HelloAlex4/Maturitaetsarbeit-Design-and-Development-of-a-Portable-Stereoscopic-Wigglegram-Camera/PCBs/mainPCB/PCB_Layout.png

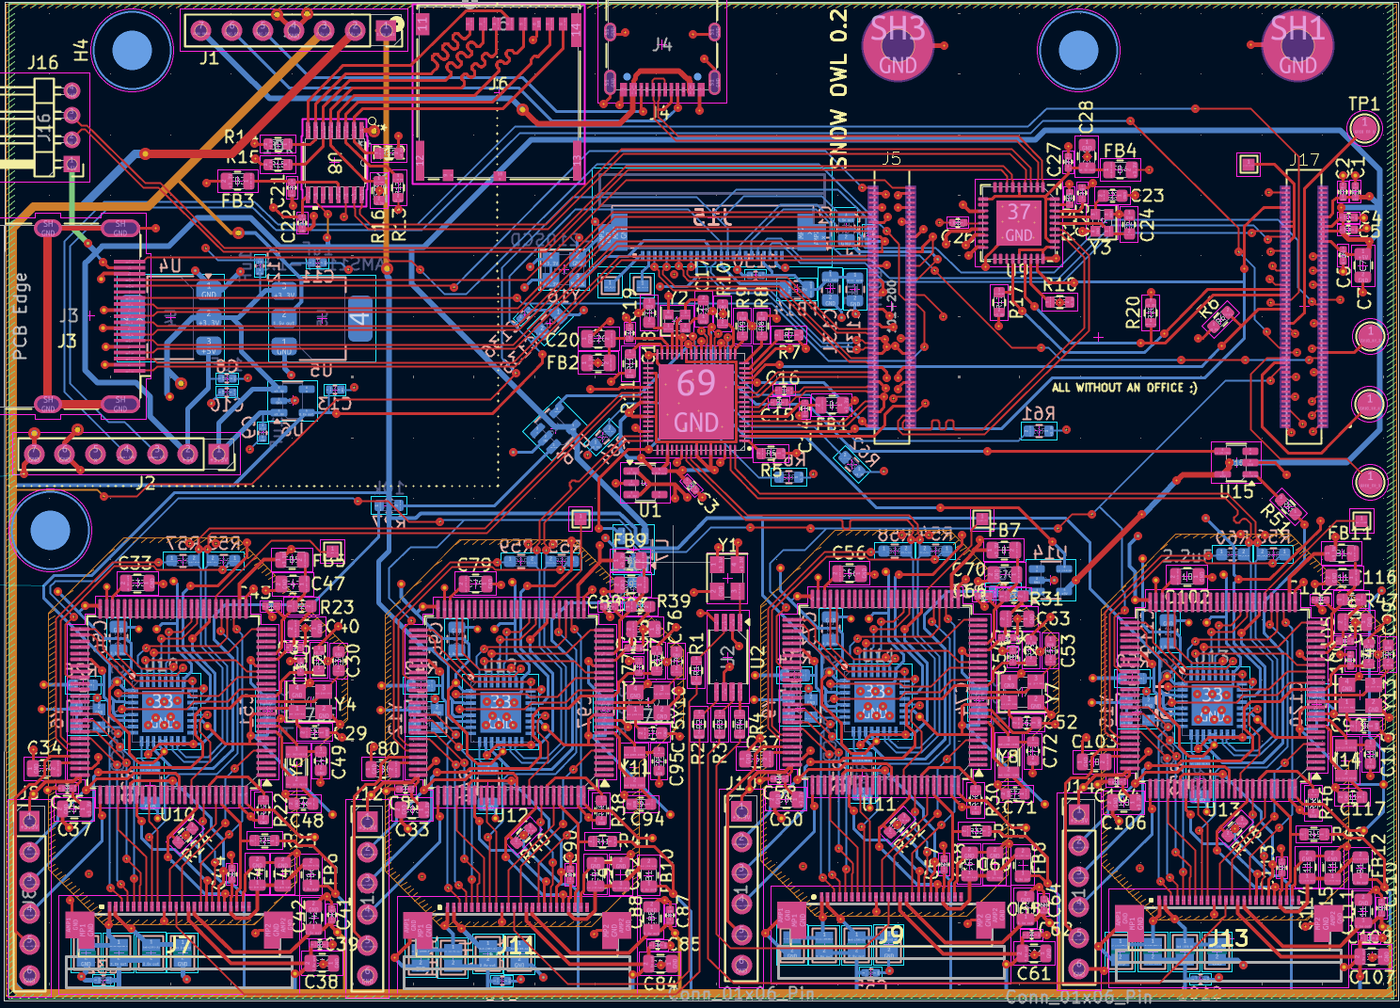
PCBs/mainPCB/PCB_Layout.png
