HelloAlex4/Maturitaetsarbeit-Design-and-Development-of-a-Portable-Stereoscopic-Wigglegram-Camera/sample_Images/wigglegram2.gif

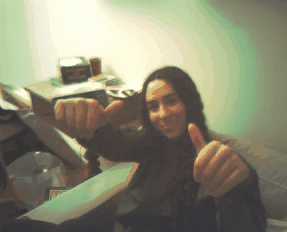
sample_Images/wigglegram2.gif
