HelloAlex4/Maturitaetsarbeit-Design-and-Development-of-a-Portable-Stereoscopic-Wigglegram-Camera/PCBs/mainPCB/kiCad Files/mainPCB.kicad_sch

## KiCad design PCBs/mainPCB/kiCad Files/mainPCB.kicad_sch (2026-01-02)

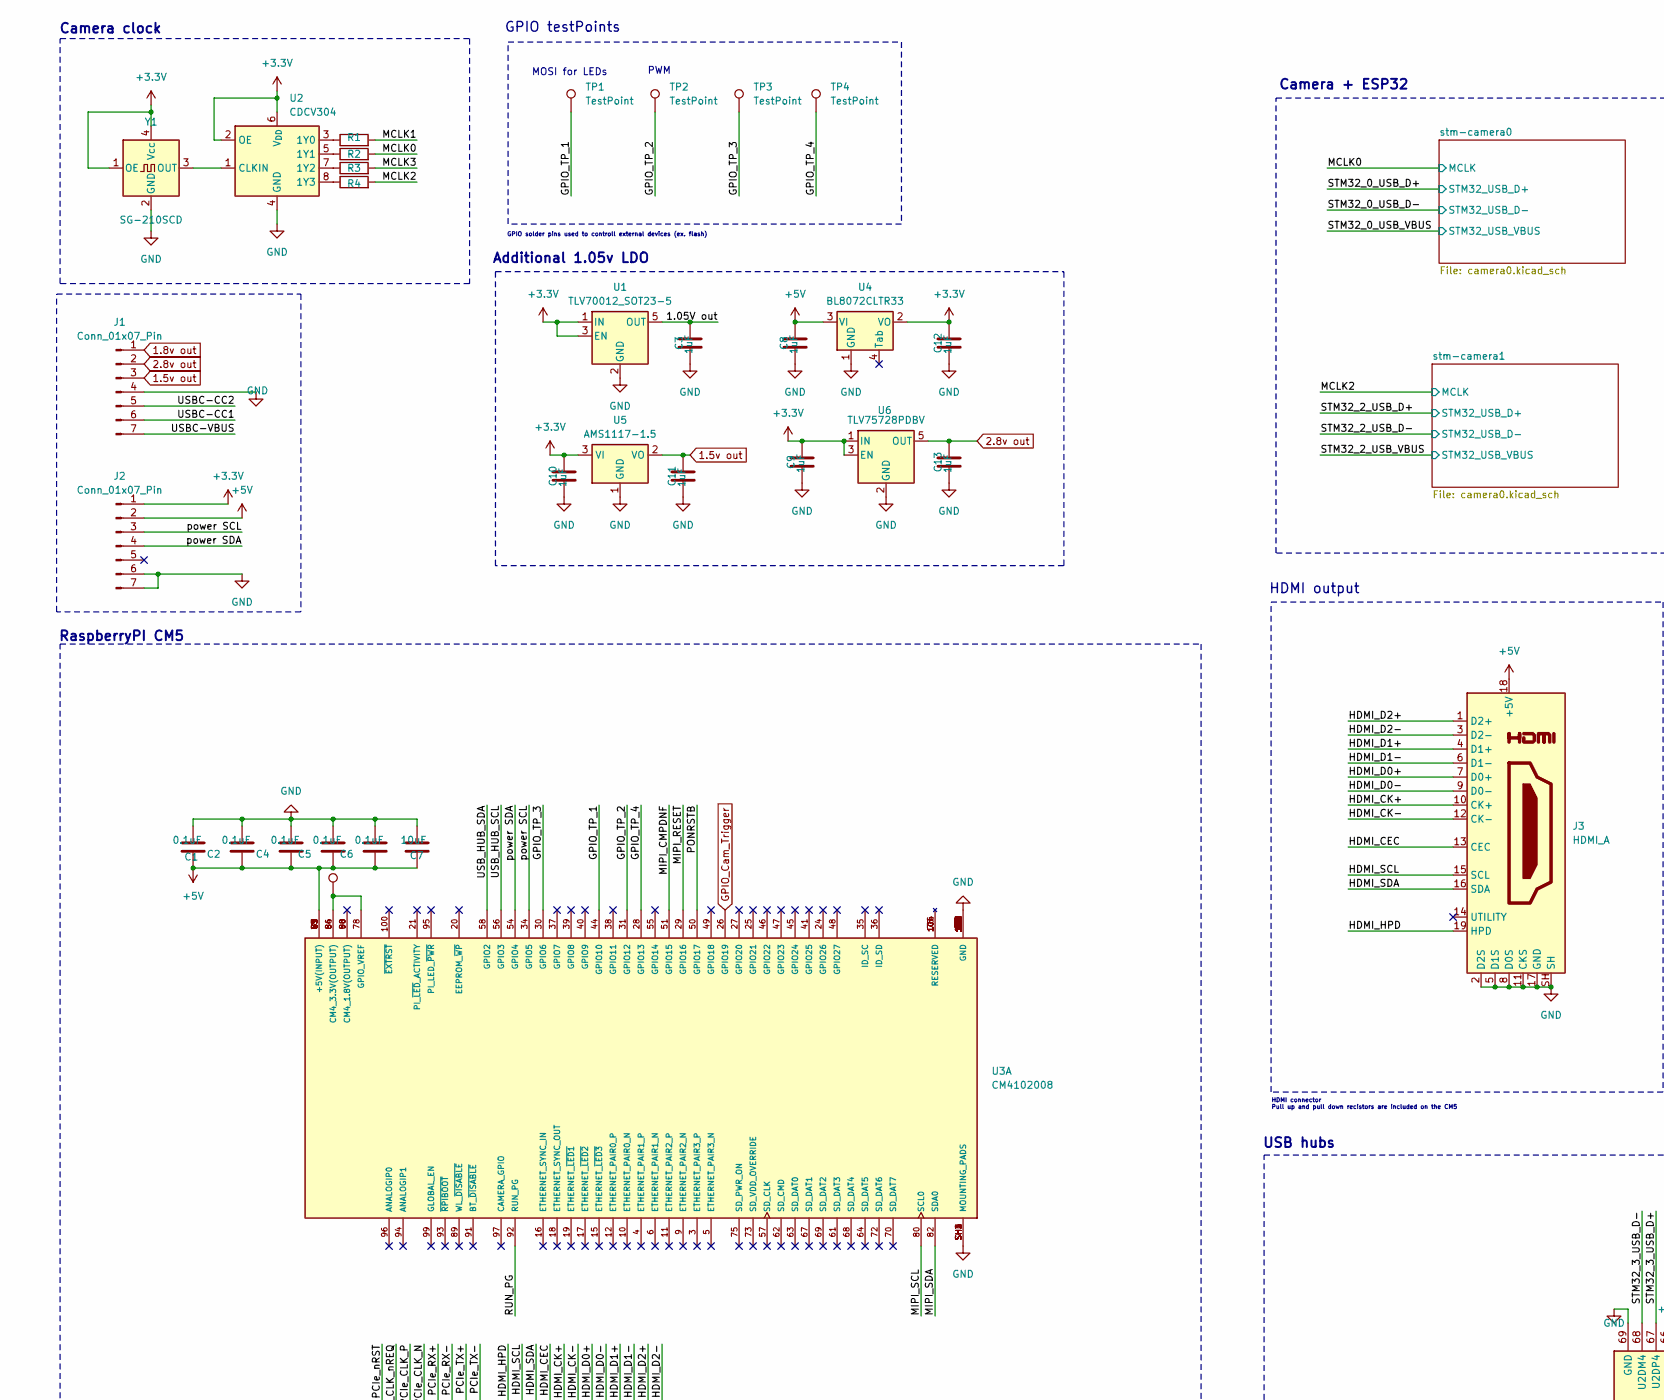
[picture p26: schematic mainPCB.kicad_sch, part in row 1, column 1]

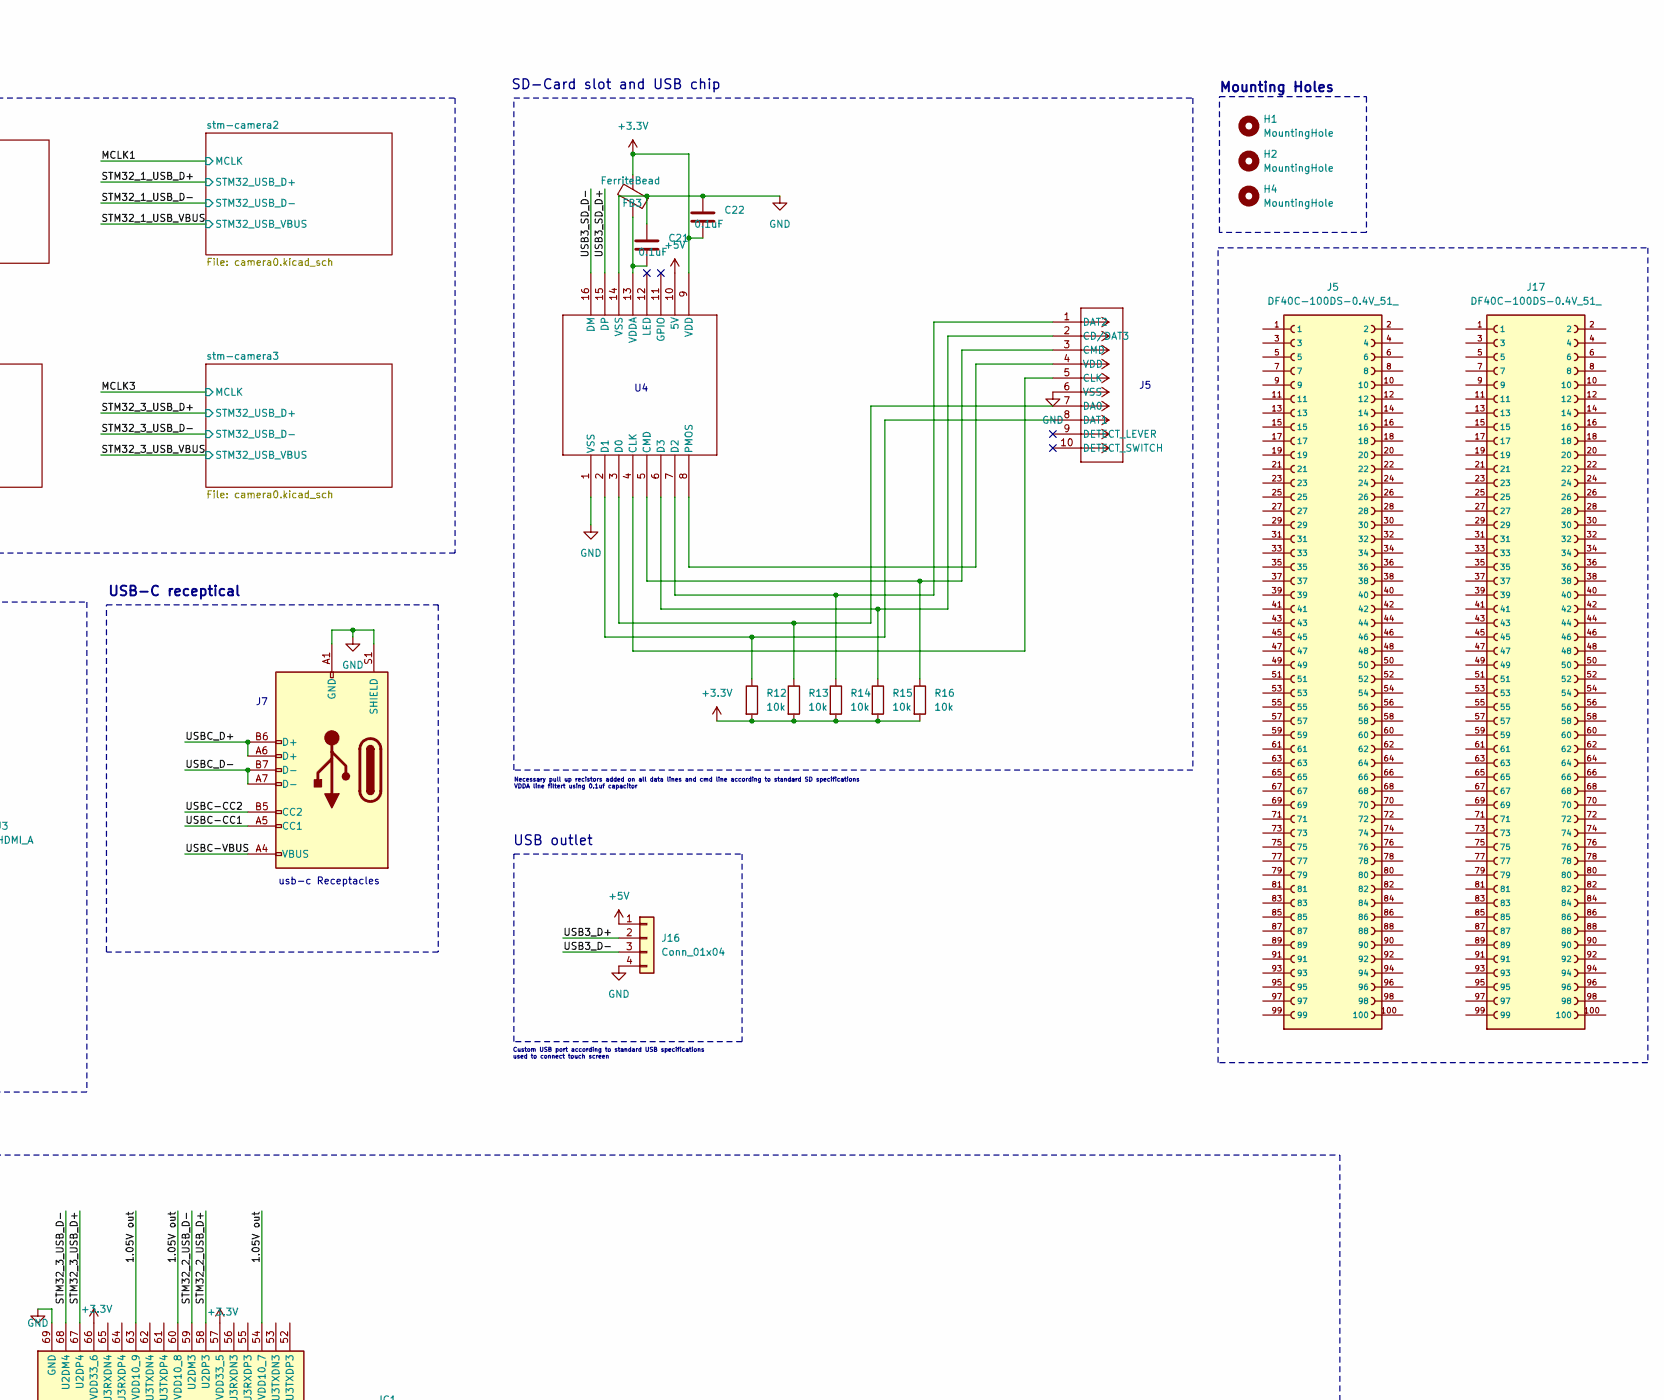
[picture p27: schematic mainPCB.kicad_sch, part in row 1, column 2]

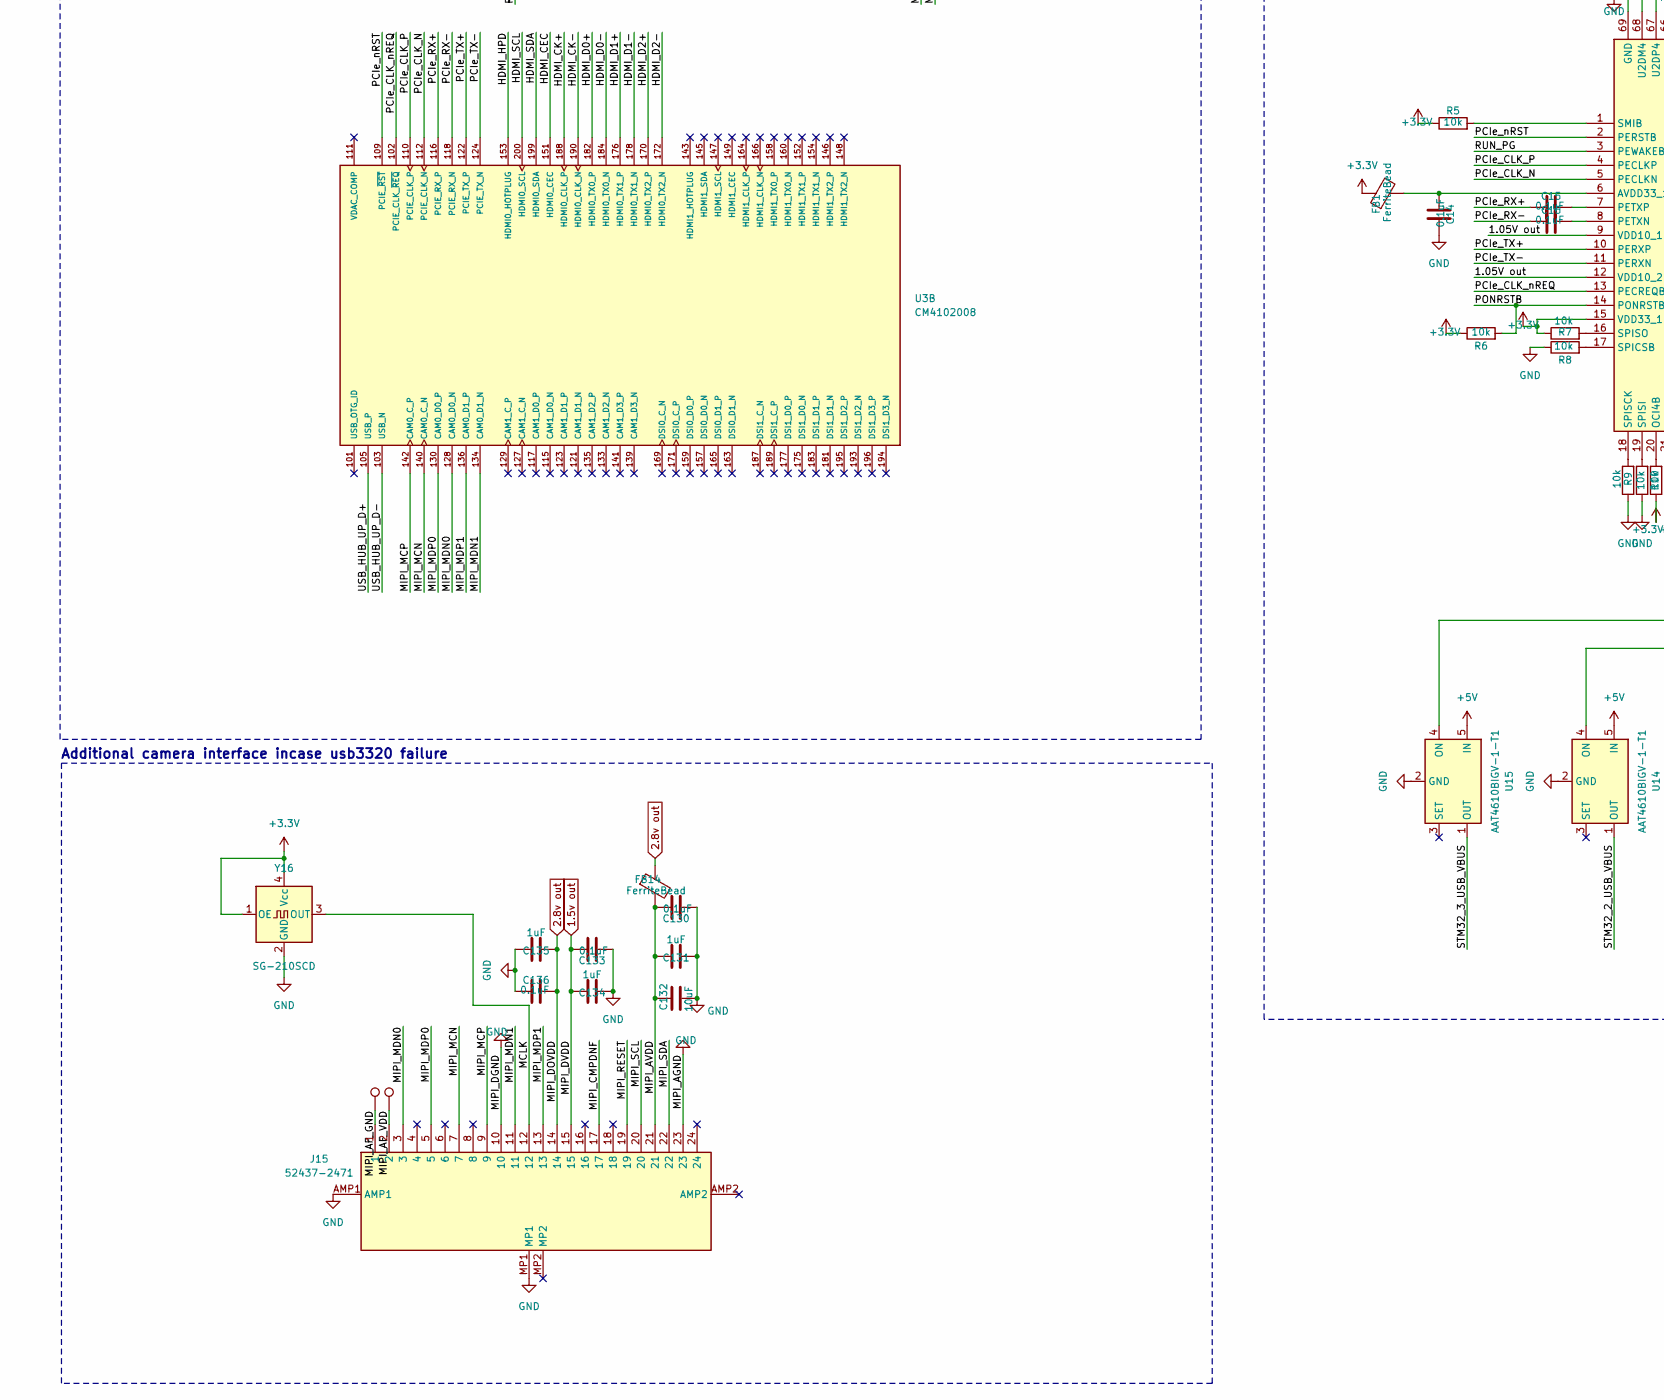
[picture p28: schematic mainPCB.kicad_sch, part in row 2, column 1]

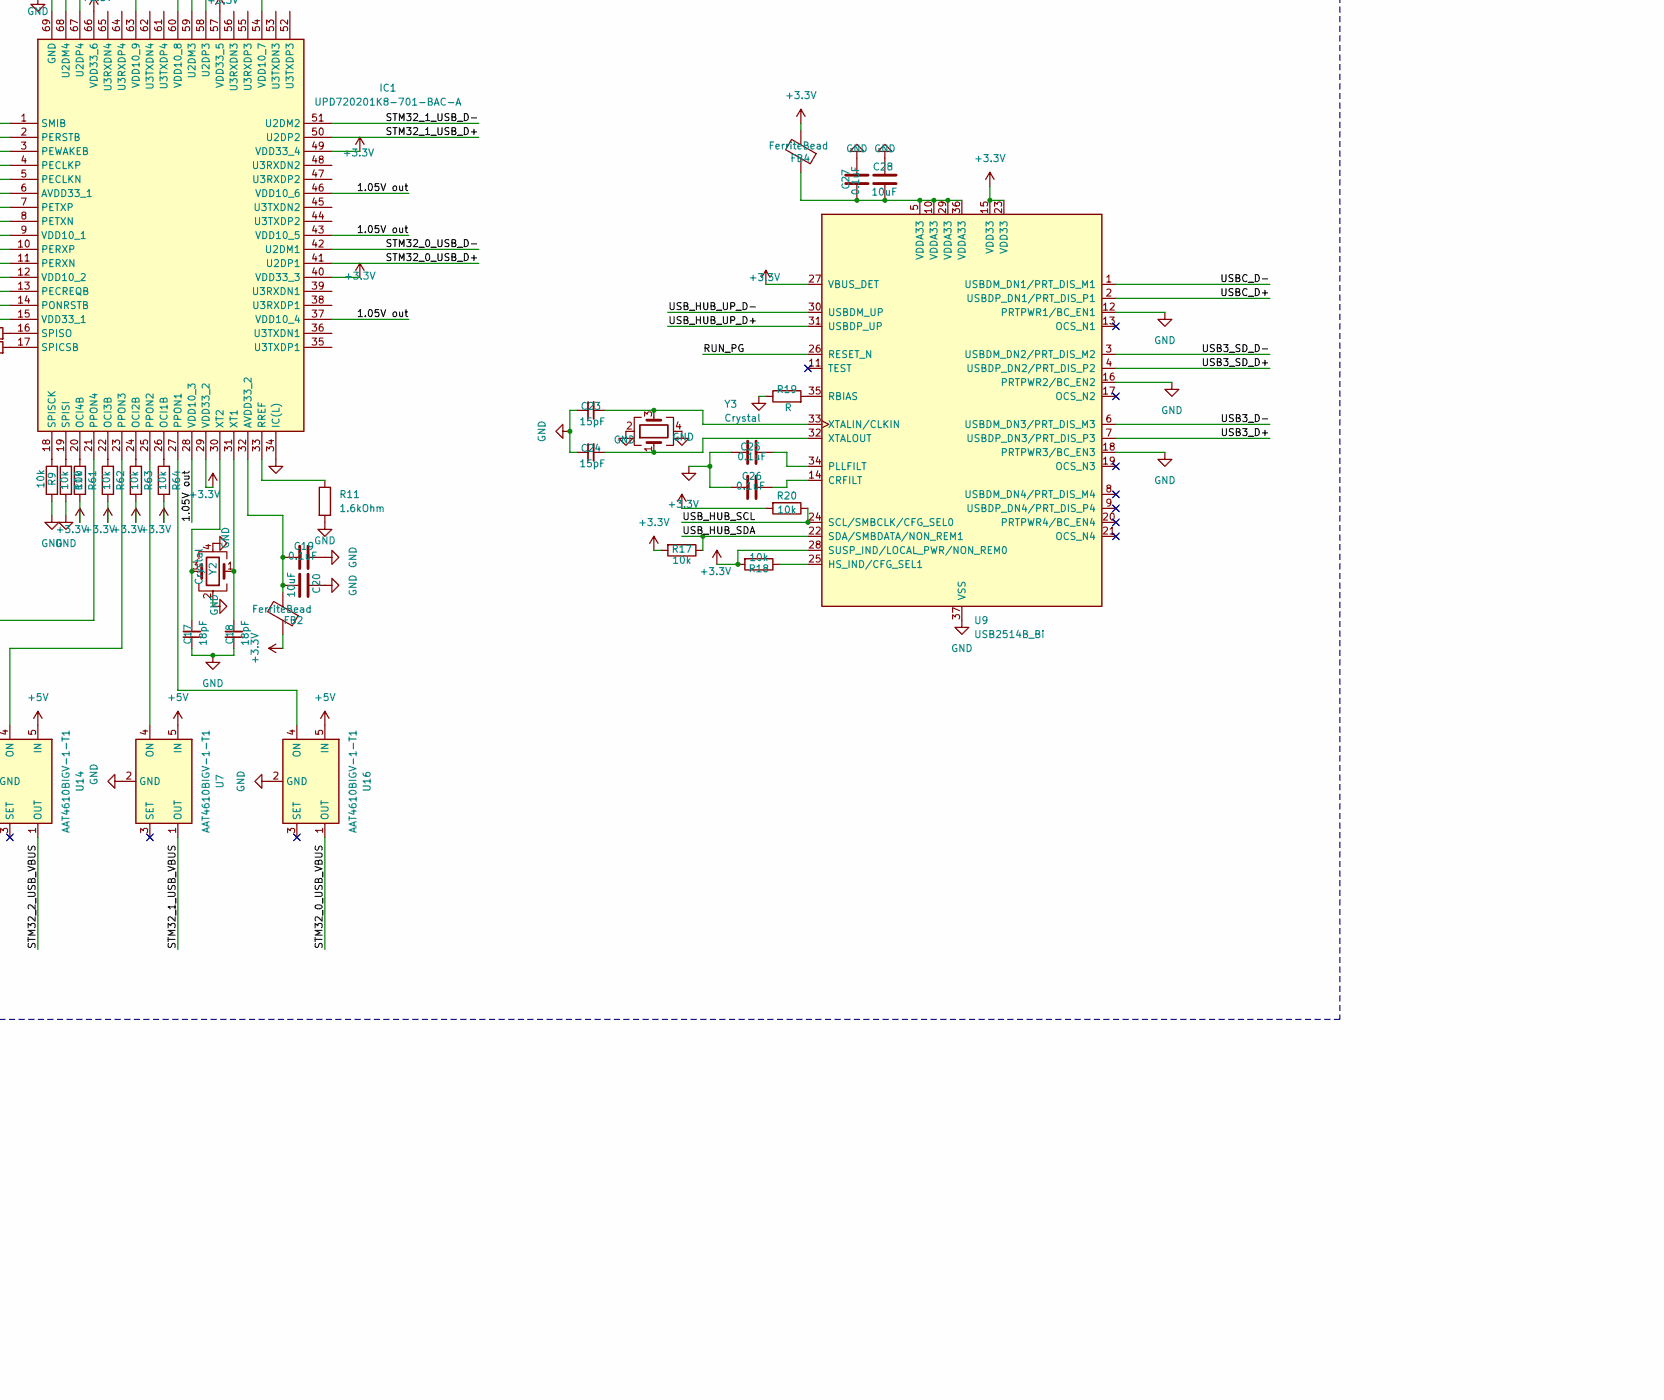
[picture p29: schematic mainPCB.kicad_sch, part in row 2, column 2]

Parts:
C1, C2, C4, C5, C6, C14, C15, C16, C19, C21, C22, C25, C26, C27, C130, C133, C136: 0.1uF; C_0402_1005Metric; manufacturer part # CL05B104KO5NNNC; LCSC Part # C1525
C3, C8, C9, C10, C11, C12, C13: 1uF; C_0402_1005Metric; manufacturer part # CL05B104KO5NNNC; LCSC Part # C14445
C7, C20, C28, C132: 10uF; C_0805_2012Metric; manufacturer part # CL21A106KAYNNNE; LCSC Part # C15850
C17, C18: 18pF; C_0603_1608Metric; manufacturer part # CL10C150JB8NNNC; LCSC Part # C1647
C23, C24: 15pF; C_0603_1608Metric; manufacturer part # CL10C150JB8NNNC; LCSC Part # C1644
C131, C134, C135: 1uF; C_0805_2012Metric; manufacturer part # CL21B105KBFNNNE; LCSC Part # C28323
FB1, FB2, FB3, FB4, FB14: FerriteBead; R_0805_2012Metric; manufacturer part # MPZ2012S601ATD25; LCSC Part # C81034
H1, H2, H4: MountingHole; MountingHole_3.2mm_M3
IC1: UPD720201K8-701-BAC-A; QFN40P800X800X90-69N-D; Mouser Part Number 968-D720201K8701BACA
J1, J2: Conn_01x07_Pin; PinSocket_1x07_P2.54mm_Vertical; LCSC Part # C2832270
J3: HDMI_A; HDMI_A_Molex_208658-1001_Horizontal; manufacturer part # 2086581001; LCSC Part # C720616
J4: USB_C_Receptacle_USB2.0_14P; USB_C_Receptacle_XKB_U262-16XN-4BVC11; manufacturer part # U262-161N-4BVC11; LCSC Part # C319148
J5, J17: DF40C-100DS-0.4V_51_; cm4100pinconnector; PARTREV Oct.1.2023; LCSC Part # C424649
J6: SD card slot; CONN_503398-1892_MOL; manufacturer part # 5033981892; LCSC Part # C428492
J15: 52437-2471; 524372471; Mouser Part Number 538-52437-2471
J16: Conn_01x04; PinHeader_1x04_P2.00mm_Horizontal; LCSC Part # C2938466
R1, R2, R3, R4: 20Ohm; R_0603_1608Metric; manufacturer part # YAGEO; LCSC Part # C23140
R5, R6, R7, R8, R9, R10, R12, R13, R14, R15, R16, R17, R18, R20, R61, R62, R63, R64: 10k; R_0603_1608Metric; manufacturer part # RC0603FR-0710KL; LCSC Part # C98220
R11: 1.6kOhm; R_0603_1608Metric; LCSC Part # C165489
R19: R; R_0402_1005Metric; LCSC Part # C102781
TP1, TP2, TP3, TP4: TestPoint; TestPoint_Pad_D2.0mm
TP5, TP6, TP11: TestPoint; TestPoint_Pad_1.0x1.0mm
U1: TLV70012_SOT23-5; SOT-23-5; LCSC Part # C469896
U2: CDCV304; TSSOP-8_4.4x3mm_P0.65mm; manufacturer part # CDCV304PWR; LCSC Part # C105237
U3: CM4102008; CM4; PARTREV 2021-10-12
U4: BL8072CLTR33; SOT-223-3_TabPin2; LCSC Part # C843780
U5: AMS1117-1.5; SOT-223-3_TabPin2; LCSC Part # C16172
U6: TLV75728PDBV; SOT-23-5; LCSC Part # C2863639
U7, U14, U15, U16: AAT4610BIGV-1-T1; SOT-23-5; LCSC Part # C517266
U8: GL823K-HCY04; SSOP-16_GL823K-HCY04_GEN; manufacturer part # GL823K-HCY04; LCSC Part # C284879
U9: USB2514B_Bi; QFN-36-1EP_6x6mm_P0.5mm_EP3.7x3.7mm; LCSC Part # C16251
Y1, Y16: SG-210SCD; Crystal_SMD_3225-4Pin_3.2x2.5mm; manufacturer part # XOS32024000LT00351005; LCSC Part # C37635416
Y2, Y3: Crystal; Crystal_SMD_2016-4Pin_2.0x1.6mm; manufacturer part # XTM20024000JT00351001; LCSC Part # C37635323

Connections:
1.05V out: C3.1, IC1.9 (VDD10_1), IC1.12 (VDD10_2), IC1.28 (VDD10_3), IC1.37 (VDD10_4), IC1.43 (VDD10_5), IC1.46 (VDD10_6), IC1.54 (VDD10_7), IC1.60 (VDD10_8), IC1.63 (VDD10_9), U1.5 (OUT)
1.5v out: C11.1, C133.1, C134.1, J1.3, J15.15, U5.2 (VO)
1.8v out: J1.1
2.8v out: C13.1, C135.2, C136.1, FB14.1, J1.2, J15.14, U6.5 (OUT)
+3.3V: C9.1, C10.1, C12.1, C22.2, FB1.1, FB2.1, FB3.2, FB4.2, IC1.15 (VDD33_1), IC1.29 (VDD33_2), IC1.40 (VDD33_3), IC1.49 (VDD33_4), IC1.57 (VDD33_5), IC1.66 (VDD33_6), J2.1, R5.1, R6.1, R7.1, R12.2, R13.2, R14.2, R15.2, R16.2, R17.2, R18.2, R20.2, R61.1, R62.1, R63.1, R64.1, U1.1 (IN), U1.3 (EN), U2.2 (OE), U2.6 (V_{DD}), U4.2 (VO), U5.3 (VI), U6.1 (IN), U6.3 (EN), U8.9 (VDD), U9.15 (VDD33), U9.23 (VDD33), U9.27 (VBUS_DET), U9.28 (SUSP_IND/LOCAL_PWR/NON_REM0), Y1.1 (OE), Y1.4 (Vcc), Y16.1 (OE), Y16.4 (Vcc)
+5V: C1.1, C2.1, C4.1, C5.1, C6.1, C7.1, C8.1, J2.2, J3.18 (+5V), J16.1, U3.77 (+5V(INPUT)), U3.79 (+5V(INPUT)), U3.81 (+5V(INPUT)), U3.83 (+5V(INPUT)), U3.85 (+5V(INPUT)), U3.87 (+5V(INPUT)), U4.3 (VI), U7.5 (IN), U8.10 (5V), U14.5 (IN), U15.5 (IN), U16.5 (IN)
GND: C1.2, C2.2, C3.2, C4.2, C5.2, C6.2, C7.2, C8.2, C9.2, C10.2, C11.2, C12.2, C13.2, C14.1, C17.1, C18.1, C19.1, C20.1, C21.2, C22.1, C23.1, C24.1, C25.2, C26.2, C27.1, C28.1, C130.2, C131.2, C132.2, C133.2, C134.2, C135.1, C136.2, IC1.34 (IC(L)), IC1.69 (GND), J1.4, J2.6, J2.7, J3.2 (D2S), J3.5 (D1S), J3.8 (D0S), J3.11 (CKS), J3.17 (GND), J3.SH, J4.A1 (GND), J4.A12 (GND), J4.B1 (GND), J4.B12 (GND), J4.S1 (SHIELD), J6.6 (VSS), J15.10, J15.23, J15.AMP1, J15.MP1, J16.4, R8.1, R9.1, R10.1, R11.2, R19.1, U1.2 (GND), U2.4 (GND), U3.1 (GND), U3.2 (GND), U3.7 (GND), U3.8 (GND), U3.13 (GND), U3.14 (GND), U3.22 (GND), U3.23 (GND), U3.32 (GND), U3.33 (GND), U3.42 (GND), U3.43 (GND), U3.52 (GND), U3.53 (GND), U3.59 (GND), U3.60 (GND), U3.65 (GND), U3.66 (GND), U3.71 (GND), U3.74 (GND), U3.98 (GND), U3.107 (GND), U3.108 (GND), U3.113 (GND), U3.114 (GND), U3.119 (GND), U3.120 (GND), U3.125 (GND), U3.126 (GND), U3.131 (GND), U3.132 (GND), U3.137 (GND), U3.138 (GND), U3.144 (GND), U3.150 (GND), U3.155 (GND), U3.156 (GND), U3.161 (GND), U3.162 (GND), U3.167 (GND), U3.168 (GND), U3.173 (GND), U3.174 (GND), U3.179 (GND), U3.180 (GND), U3.185 (GND), U3.186 (GND), U3.191 (GND), U3.192 (GND), U3.197 (GND), U3.198 (GND), U3.SH1 (MOUNTING_PADS), U3.SH2 (MOUNTING_PADS), U3.SH3 (MOUNTING_PADS), U3.SH4 (MOUNTING_PADS), U4.1 (GND), U5.1 (GND), U6.2 (GND), U7.2 (GND), U8.1 (VSS), U8.14 (VSS), U9.12 (PRTPWR1/BC_EN1), U9.16 (PRTPWR2/BC_EN2), U9.18 (PRTPWR3/BC_EN3), U9.37 (VSS), U14.2 (GND), U15.2 (GND), U16.2 (GND), Y1.2 (GND), Y2.2, Y2.4, Y3.2, Y3.4, Y16.2 (GND)
GPIO_Cam_Trigger: U3.26 (GPIO19)
GPIO_TP_1: TP1.1, U3.44 (GPIO10)
GPIO_TP_2: TP2.1, U3.31 (GPIO12)
GPIO_TP_3: TP3.1, U3.30 (GPIO6)
GPIO_TP_4: TP4.1, U3.28 (GPIO13)
HDMI_CEC: J3.13 (CEC), U3.151 (HDMI0_CEC)
HDMI_CK+: J3.10 (CK+), U3.188 (HDMI0_CLK_P)
HDMI_CK-: J3.12 (CK-), U3.190 (HDMI0_CLK_N)
HDMI_D0+: J3.7 (D0+), U3.182 (HDMI0_TX0_P)
HDMI_D0-: J3.9 (D0-), U3.184 (HDMI0_TX0_N)
HDMI_D1+: J3.4 (D1+), U3.176 (HDMI0_TX1_P)
HDMI_D1-: J3.6 (D1-), U3.178 (HDMI0_TX1_N)
HDMI_D2+: J3.1 (D2+), U3.170 (HDMI0_TX2_P)
HDMI_D2-: J3.3 (D2-), U3.172 (HDMI0_TX2_N)
HDMI_HPD: J3.19 (HPD), U3.153 (HDMI0_HOTPLUG)
HDMI_SCL: J3.15 (SCL), U3.200 (HDMI0_SCL)
HDMI_SDA: J3.16 (SDA), U3.199 (HDMI0_SDA)
MCLK: J15.12, Y16.3 (OUT)
MCLK0: R2.2
MCLK1: R1.2
MCLK2: R4.2
MCLK3: R3.2
MIPI_AF_GND: J15.1, TP5.1
MIPI_AF_VDD: J15.2, TP6.1
MIPI_AVDD: C130.1, C131.1, C132.1, FB14.2, J15.21
MIPI_CMPDNF: J15.17, U3.51 (GPIO15)
MIPI_MCN: J15.7, U3.140 (CAM0_C_N)
MIPI_MCP: J15.9, U3.142 (CAM0_C_P)
MIPI_MDN0: J15.3, U3.128 (CAM0_D0_N)
MIPI_MDN1: J15.11, U3.134 (CAM0_D1_N)
MIPI_MDP0: J15.5, U3.130 (CAM0_D0_P)
MIPI_MDP1: J15.13, U3.136 (CAM0_D1_P)
MIPI_RESET: J15.19, U3.29 (GPIO16)
MIPI_SCL: J15.20, U3.80 (SCL0)
MIPI_SDA: J15.22, U3.82 (SDA0)
unnamed: C14.2, FB1.2, IC1.6 (AVDD33_1)
unnamed: C15.1, IC1.7 (PETXP)
unnamed: C16.1, IC1.8 (PETXN)
unnamed: C17.2, IC1.30 (XT2), Y2.3
unnamed: C18.2, IC1.31 (XT1), Y2.1
unnamed: C19.2, C20.2, FB2.2, IC1.32 (AVDD33_2)
unnamed: C21.1, FB3.1, U8.13 (VDDA)
unnamed: C23.2, U9.33 (XTALIN/CLKIN), Y3.3
unnamed: C24.2, U9.32 (XTALOUT), Y3.1
unnamed: C25.1, U9.34 (PLLFILT)
unnamed: C26.1, U9.14 (CRFILT)
unnamed: C27.2, C28.2, FB4.1, U9.5 (VDDA33), U9.10 (VDDA33), U9.29 (VDDA33), U9.36 (VDDA33)
unnamed: IC1.1 (SMIB), R5.2
unnamed: IC1.16 (SPISO), R7.2
unnamed: IC1.17 (SPICSB), R8.2
unnamed: IC1.18 (SPISCK), R9.2
unnamed: IC1.19 (SPISI), R10.2
unnamed: IC1.20 (OCI4B), R61.2
unnamed: IC1.21 (PPON4), U15.4 (ON)
unnamed: IC1.22 (OCI3B), R62.2
unnamed: IC1.23 (PPON3), U14.4 (ON)
unnamed: IC1.24 (OCI2B), R63.2
unnamed: IC1.25 (PPON2), U7.4 (ON)
unnamed: IC1.26 (OCI1B), R64.2
unnamed: IC1.27 (PPON1), U16.4 (ON)
unnamed: IC1.33 (RREF), R11.1
unnamed: J6.1 (DAT2), R14.1, U8.7 (D2)
unnamed: J6.2 (CD/DAT3), R15.1, U8.6 (D3)
unnamed: J6.3 (CMD), R16.1, U8.5 (CMD)
unnamed: J6.4 (VDD), U8.8 (PMOS)
unnamed: J6.5 (CLK), U8.4 (CLK)
unnamed: J6.7 (DA0), R13.1, U8.3 (D0)
unnamed: J6.8 (DAT1), R12.1, U8.2 (D1)
unnamed: R1.1, U2.3 (1Y0)
unnamed: R2.1, U2.5 (1Y1)
unnamed: R3.1, U2.7 (1Y2)
unnamed: R4.1, U2.8 (1Y3)
unnamed: R18.1, U9.25 (HS_IND/CFG_SEL1)
unnamed: R19.2, U9.35 (RBIAS)
unnamed: TP11.1, U3.78 (GPIO_VREF), U3.84 (CM4_3.3V(OUTPUT)), U3.86 (CM4_3.3V(OUTPUT))
unnamed: U2.1 (CLKIN), Y1.3 (OUT)
unnamed: U3.88 (CM4_1.8V(OUTPUT)), U3.90 (CM4_1.8V(OUTPUT))
unnamed: U3.76 (RESERVED), U3.104 (RESERVED), U3.106 (RESERVED)
PCIe_CLK_N: IC1.5 (PECLKN), U3.112 (PCIE_CLK_N)
PCIe_CLK_P: IC1.4 (PECLKP), U3.110 (PCIE_CLK_P)
PCIe_CLK_nREQ: IC1.13 (PECREQB), U3.102 (PCIE_CLK_~REQ)
PCIe_RX+: C15.2, U3.116 (PCIE_RX_P)
PCIe_RX-: C16.2, U3.118 (PCIE_RX_N)
PCIe_TX+: IC1.10 (PERXP), U3.122 (PCIE_TX_P)
PCIe_TX-: IC1.11 (PERXN), U3.124 (PCIE_TX_N)
PCIe_nRST: IC1.2 (PERSTB), U3.109 (PCIE_~RST)
PONRSTB: IC1.14 (PONRSTB), R6.2, U3.50 (GPIO17)
RUN_PG: IC1.3 (PEWAKEB), U3.92 (RUN_PG), U9.26 (RESET_N)
STM32_0_USB_D+: IC1.41 (U2DP1)
STM32_0_USB_D-: IC1.42 (U2DM1)
STM32_0_USB_VBUS: U16.1 (OUT)
STM32_1_USB_D+: IC1.50 (U2DP2)
STM32_1_USB_D-: IC1.51 (U2DM2)
STM32_1_USB_VBUS: U7.1 (OUT)
STM32_2_USB_D+: IC1.58 (U2DP3)
STM32_2_USB_D-: IC1.59 (U2DM3)
STM32_2_USB_VBUS: U14.1 (OUT)
STM32_3_USB_D+: IC1.67 (U2DP4)
STM32_3_USB_D-: IC1.68 (U2DM4)
STM32_3_USB_VBUS: U15.1 (OUT)
USB3_D+: J16.2, U9.7 (USBDP_DN3/PRT_DIS_P3)
USB3_D-: J16.3, U9.6 (USBDM_DN3/PRT_DIS_M3)
USB3_SD_D+: U8.15 (DP), U9.4 (USBDP_DN2/PRT_DIS_P2)
USB3_SD_D-: U8.16 (DM), U9.3 (USBDM_DN2/PRT_DIS_M2)
USBC-CC1: J1.6, J4.A5 (CC1)
USBC-CC2: J1.5, J4.B5 (CC2)
USBC-VBUS: J1.7, J4.A4 (VBUS), J4.A9 (VBUS), J4.B4 (VBUS), J4.B9 (VBUS)
USBC_D+: J4.A6 (D+), J4.B6 (D+), U9.2 (USBDP_DN1/PRT_DIS_P1)
USBC_D-: J4.A7 (D-), J4.B7 (D-), U9.1 (USBDM_DN1/PRT_DIS_M1)
USB_HUB_SCL: R20.1, U3.56 (GPIO3), U9.24 (SCL/SMBCLK/CFG_SEL0)
USB_HUB_SDA: R17.1, U3.58 (GPIO2), U9.22 (SDA/SMBDATA/NON_REM1)
USB_HUB_UP_D+: U3.105 (USB_P), U9.31 (USBDP_UP)
USB_HUB_UP_D-: U3.103 (USB_N), U9.30 (USBDM_UP)
power SCL: J2.3, U3.34 (GPIO5)
power SDA: J2.4, U3.54 (GPIO4)

Notes on the sheet:
Custom USB port according to standard USB specifications used to connect touch screen
HDMI output
RaspberryPI CM5
GPIO solder pins used to controll external devices (ex. flash)
USB outlet
Camera clock
MOSI for LEDs
PWM
HDMI connector Pull up and pull down recistors are included on the CM5
usb-c Receptacles
Mounting Holes
GPIO testPoints
SD-Card slot and USB chip
Necessary pull up recistors added on all data lines and cmd line according to standard SD specifications VDDA line filtert using 0.1uf capacitor
USB-C receptical
Camera + ESP32
Additional camera interface incase usb3320 failure
USB hubs
Additional 1.05v LDO
